Mic-Tsai/HECS_Electronic-Pixel_U/Pixel-U_Image/Pixel-120/frame007.bmp

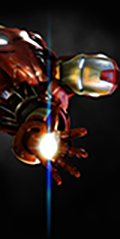
Pixel-U_Image/Pixel-120/frame007.bmp
