Mic-Tsai/HECS_Electronic-Pixel_U/Pixel-U_Image/Pixel-U_EFFA_2018/frame000.bmp

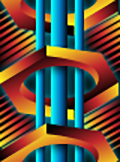
Pixel-U_Image/Pixel-U_EFFA_2018/frame000.bmp
